The8BitEnthusiast/uart-tx-module/schematics/UART.kicad_sch

## KiCad design schematics/UART.kicad_sch (2024-01-17)

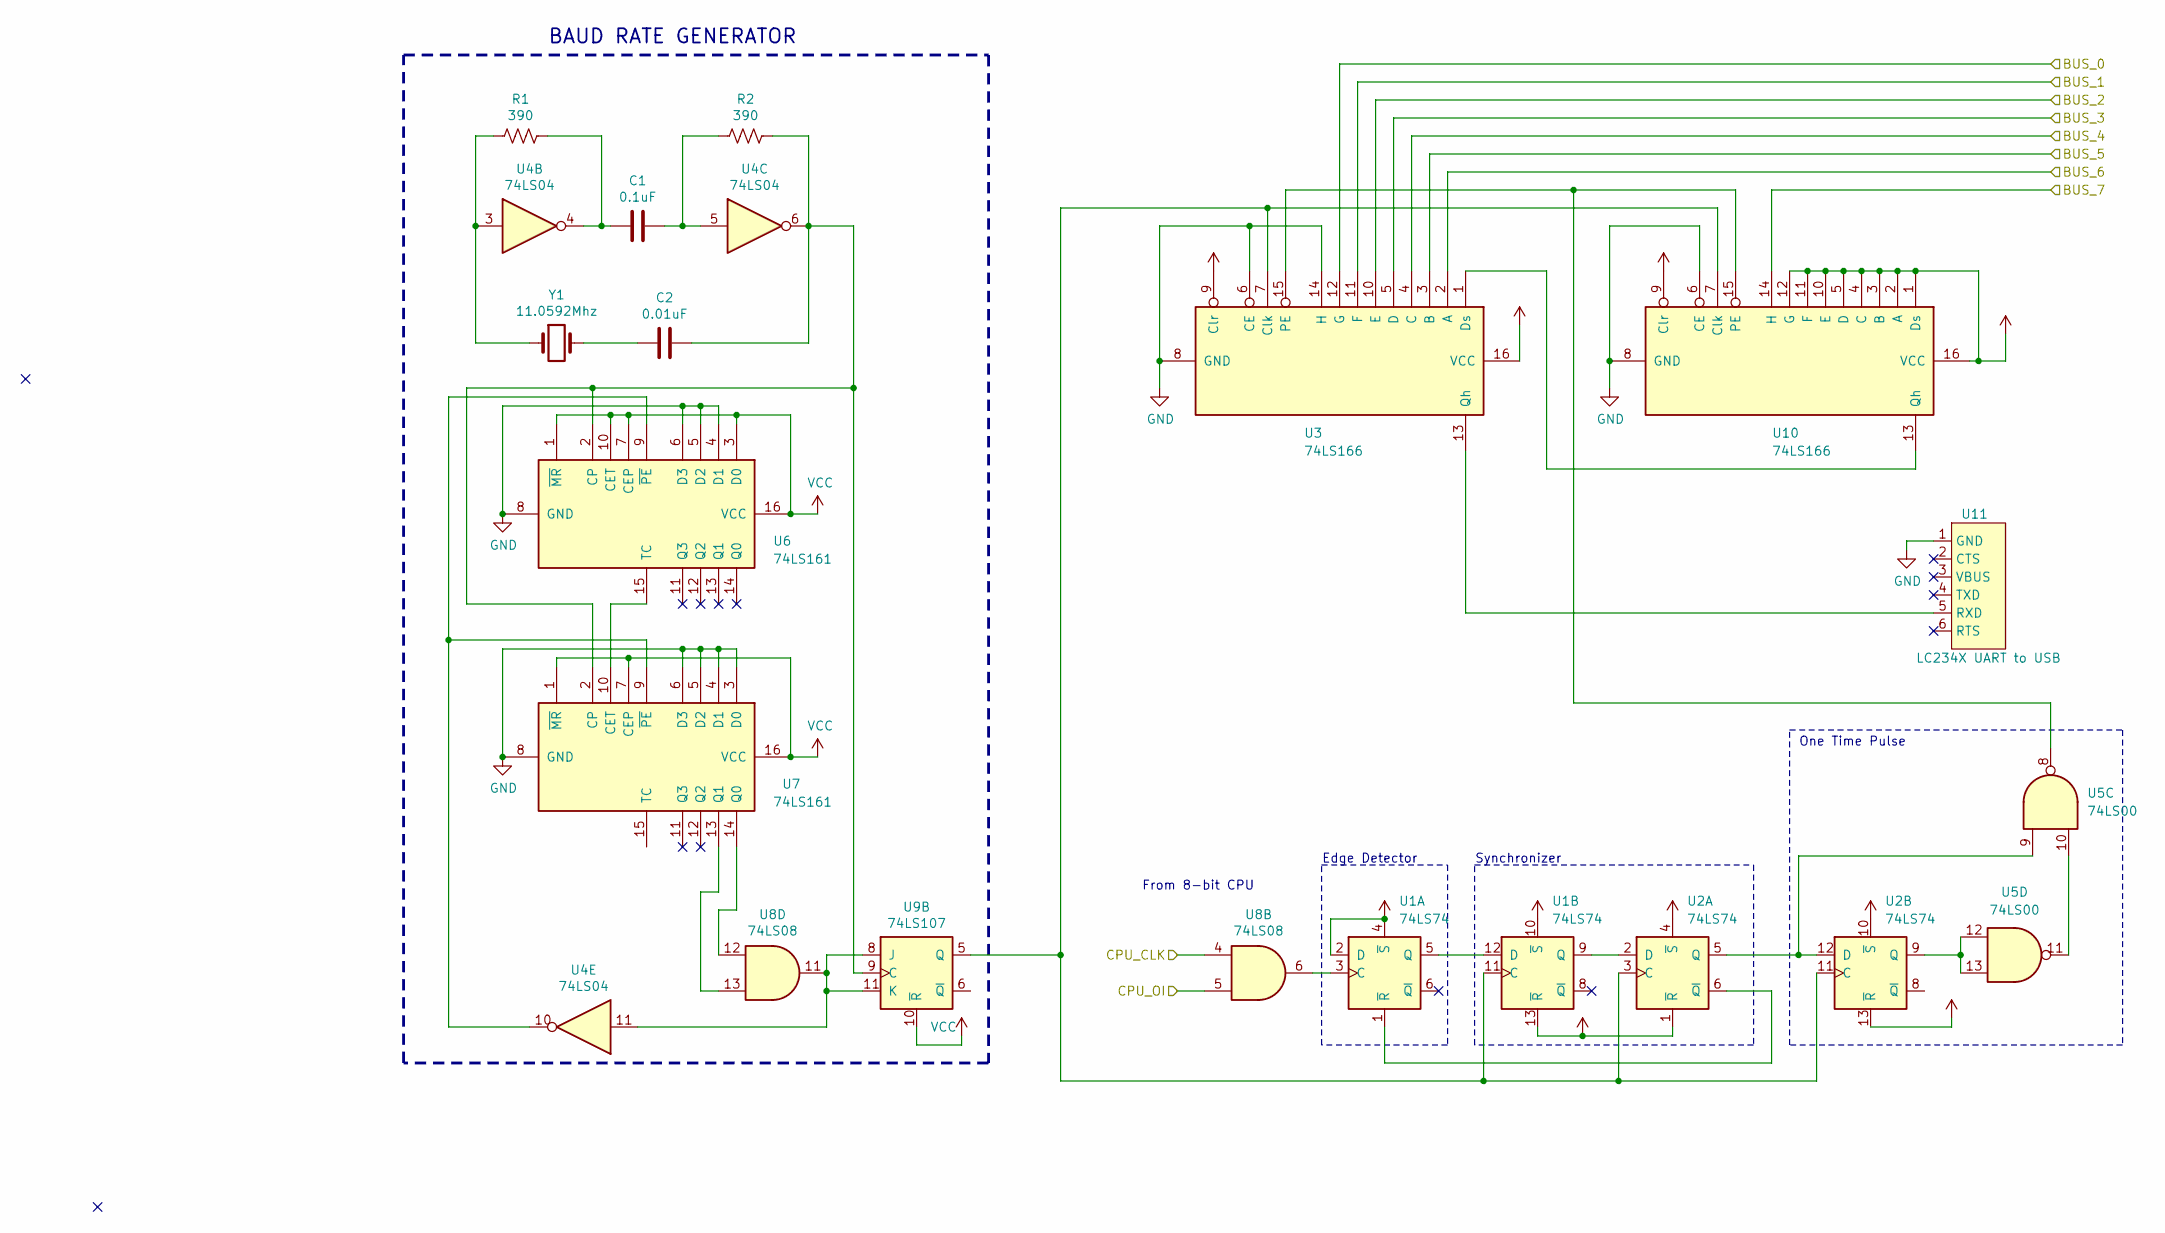
[picture p5: schematic UART.kicad_sch]

Parts:
C1: 0.1uF
C2: 0.01uF
R1, R2: 390
U1, U2: 74LS74
U3, U10: 74LS166
U4: 74LS04
U5: 74LS00
U6, U7: 74LS161
U8: 74LS08
U9: 74LS107
U11: LC234X UART to USB
Y1: 11.0592Mhz

Connections:
BUS_0: U3.12 (G)
BUS_1: U3.11 (F)
BUS_2: U3.10 (E)
BUS_3: U3.5 (D)
BUS_4: U3.4 (C)
BUS_5: U3.3 (B)
BUS_6: U3.2 (A)
BUS_7: U10.14 (H)
CPU_CLK: U8.4
CPU_OI: U8.5
GND: U3.6 (CE), U3.8 (GND), U3.14 (H), U6.4 (D1), U6.5 (D2), U6.6 (D3), U6.8 (GND), U7.3 (D0), U7.4 (D1), U7.5 (D2), U7.6 (D3), U7.8 (GND), U10.6 (CE), U10.8 (GND), U11.1 (GND)
unnamed: C1.1, R2.2, U4.5
unnamed: C1.2, R1.1, U4.4
unnamed: C2.1, Y1.2
unnamed: C2.2, R2.1, U4.6, U6.2 (CP), U7.2 (CP), U9.9 (C)
unnamed: R1.2, U4.3, Y1.1
unnamed: U1.1 (~R), U2.6 (~Q)
unnamed: U1.3 (C), U8.6
unnamed: U1.9 (Q), U2.2 (D)
unnamed: U1.11 (C), U2.3 (C), U2.11 (C), U3.7 (Clk), U9.5 (Q), U10.7 (Clk)
unnamed: U1.5 (Q), U1.12 (D)
unnamed: U2.9 (Q), U5.12, U5.13
unnamed: U2.5 (Q), U2.12 (D), U5.9
unnamed: U4.10, U6.9 (~PE), U7.9 (~PE)
unnamed: U4.11, U8.11, U9.8 (J), U9.11 (K)
unnamed: U5.10, U5.11
unnamed: U6.15 (TC), U7.10 (CET)
unnamed: U7.13 (Q1), U8.13
unnamed: U7.14 (Q0), U8.12
unnamed: U3.1 (Ds), U10.13 (Qh)
unnamed: U3.15 (PE), U5.8, U10.15 (PE)
unnamed: U3.13 (Qh), U11.5 (RXD)
VCC: U1.2 (D), U1.4 (~S), U1.10 (~S), U1.13 (~R), U2.1 (~R), U2.4 (~S), U2.10 (~S), U2.13 (~R), U3.9 (Clr), U3.16 (VCC), U6.1 (~MR), U6.3 (D0), U6.7 (CEP), U6.10 (CET), U6.16 (VCC), U7.1 (~MR), U7.7 (CEP), U7.16 (VCC), U9.10 (~R), U10.1 (Ds), U10.2 (A), U10.3 (B), U10.4 (C), U10.5 (D), U10.9 (Clr), U10.10 (E), U10.11 (F), U10.12 (G), U10.16 (VCC)

Notes on the sheet:
Edge Detector
Synchronizer
From 8-bit CPU
BAUD RATE GENERATOR
One Time Pulse
